mlp6/ADPL/software/cloud-dashboard/node-server/coverage/lcov-report/node-server/models/bucket-event.js.html

# All files / node-server/models bucket-event.js

100% Statements 4/4

100% Branches 0/0

100% Functions 0/0

100% Lines 4/4

1
2
3
4
5
6
7
8
9
10
11
12
13
14
15
16
17

1x
1x
1x

1x

/*
* bucket-event.js
* The schema to hold incoming bucket
* tip events from ADPL sites.
* @author: Suyash Kumar <suyashkumar2003@gmail.com>
*/
var mongoose = require('mongoose');
var Schema = mongoose.Schema;
var BucketEvent = new Schema({
coreid: {type: String, required: true, trim: true}, // Particle core id of sender
loc: {type: String, required: true, trim: true}, // Location identifier
time: {type: Date, required: true}, // Datetime of publish
data: {type: Number, required: false}, // typically a tip count since reset
});

module.exports = mongoose.model('BucketEvent', BucketEvent);

Code coverage generated by istanbul (http://istanbul-js.org/) at Wed Jan 18 2017 23:22:50 GMT-0800 (PST)
