mlp6/ADPL/software/cloud-dashboard/node-server/coverage/lcov-report/node-server/models/temperature-event.js.html

# All files / node-server/models temperature-event.js

100% Statements 4/4

100% Branches 0/0

100% Functions 0/0

100% Lines 4/4

1
2
3
4
5
6
7
8
9
10
11
12
13
14
15
16
17
18
19
20
21
22
23
24

2x
2x
2x

2x

/*
* temperature-event.js
* The schema (and model) to hold incoming
* temperature log events
* @author: Suyash Kumar <suyashkumar2003@gmail.com>
*/
var mongoose = require('mongoose');
var Schema = mongoose.Schema;
var TemperatureEvent = new Schema({
coreid: {type: String, required: true, trim: true}, // coreid of sender
loc: {type: String, required: true, trim: true}, // Location identifier
time: {type: Date, required: true}, // Time the data was published
temps: {
HXCI: {type: Number, required: false},
HXCO: {type: Number, required: false},
HTR: {type: Number, required: false},
HXHI: {type: Number, required: false},
HXHO: {type: Number, required: false},
},
valveStatus: {type: Boolean, required: false}, // Valve status at this event's time
});

module.exports = mongoose.model('TemperatureEvent', TemperatureEvent);

Code coverage generated by istanbul (http://istanbul-js.org/) at Wed Jan 18 2017 23:22:50 GMT-0800 (PST)
