mlp6/ADPL/hardware/picture_aids/FieldPics/IMG_2328.JPG

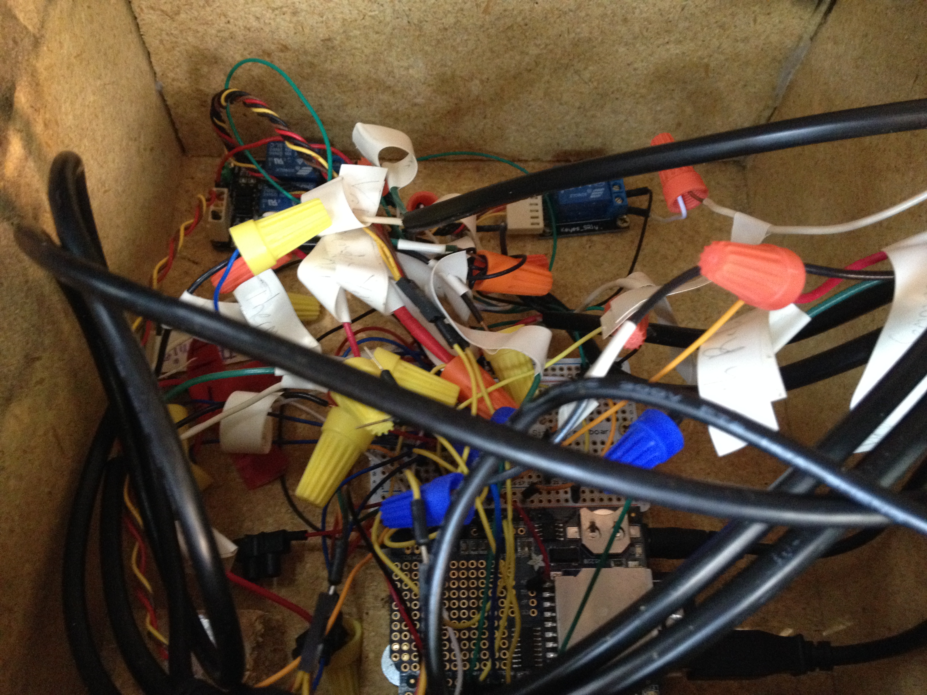
hardware/picture_aids/FieldPics/IMG_2328.JPG
