mlp6/ADPL/hardware/picture_aids/FieldPics/IMG_2395.JPG

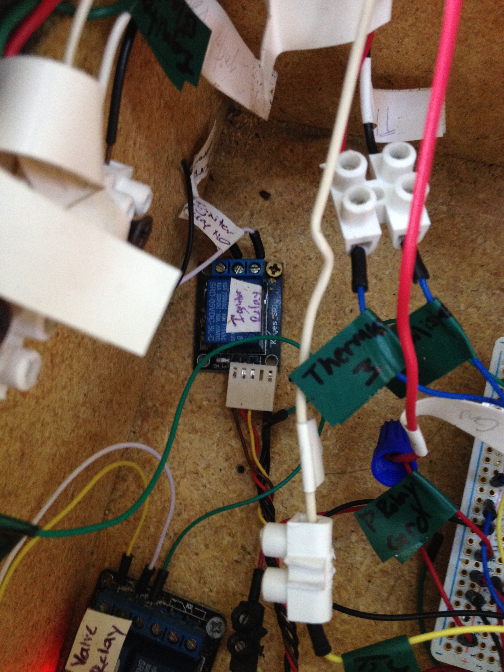
hardware/picture_aids/FieldPics/IMG_2395.JPG
