mlp6/ADPL/hardware/picture_aids/FieldPics/IMG_2436.JPG

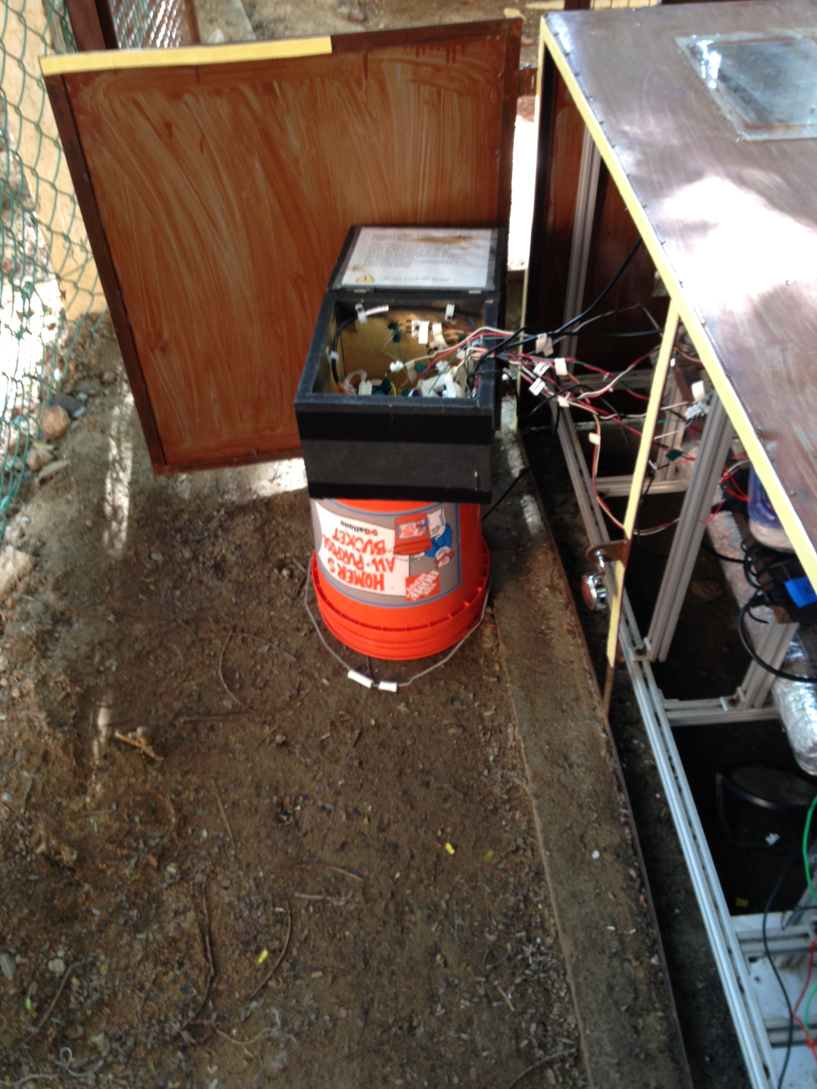
hardware/picture_aids/FieldPics/IMG_2436.JPG
