mlp6/ADPL/hardware/picture_aids/FieldPics/IMG_7628.JPG

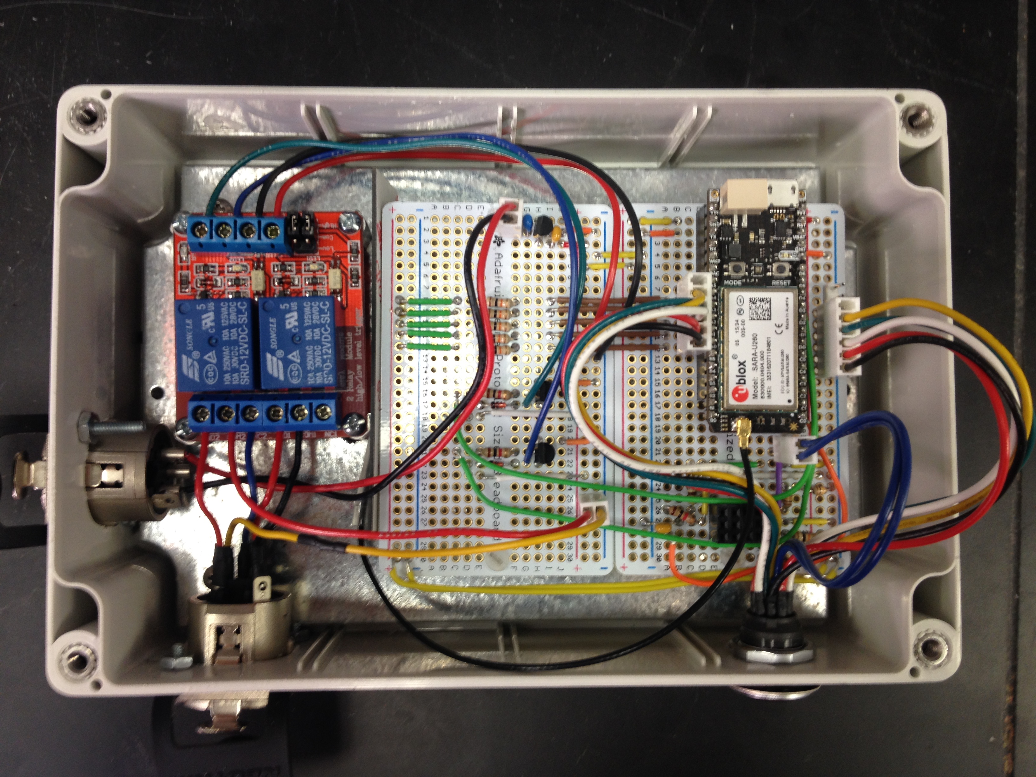
hardware/picture_aids/FieldPics/IMG_7628.JPG
