mlp6/ADPL/software/cloud-dashboard/node-server/coverage/lcov-report/node-server/tests/handle-device/test-data.js.html

# All files / node-server/tests/handle-device test-data.js

100% Statements 4/4

100% Branches 0/0

100% Functions 0/0

100% Lines 4/4

1
2
3
4
5
6
7
8
9
10
11
12
13

1x

1x

1x

1x

const sampleTempEvent = {data: '{"data":"HXCI:-73.9,HXCO:-75.7,HTR:-74.7,HXHI:-75.1,HXHO:-74.9,V:0","ttl":"60","published_at":"2017-01-19T06:45:44.999Z","coreid":"400057000a51343334363138"}'}

const sampleBucketEvent = {data: {"data":"0","ttl":"60","published_at":"2017-01-19T06:35:03.110Z","coreid":"2d0042000951343334363138"}};

const tempEventParsedData = {"HTR": "-74.7", "HXCI": "-73.9", "HXCO": "-75.7", "HXHI": "-75.1", "HXHO": "-74.9", "V": "0", "coreid": "400057000a51343334363138", "published_at": "2017-01-19T06:45:44.999Z"}

module.exports = {
sampleTempEvent,
sampleBucketEvent,
tempEventParsedData
}

Code coverage generated by istanbul (http://istanbul-js.org/) at Wed Jan 18 2017 23:22:50 GMT-0800 (PST)
