mlp6/ADPL/software/ADPL_electron/PinchValve.h

#ifndef ADPL_PINCHVALVE_H
#define ADPL_PINCHVALVE_H

class PinchValve{

    public:
        PinchValve(int dir_pin, int step_pin, int sleep_pin, int up_pin, int down_pin, int reset_pin);
        void shiftUp(double res);
        void shiftDown(double res);
        volatile bool moveup;
        volatile bool movedown;
        volatile bool isitup;
        unsigned long wait_time = 0;
        double position;
        double resolution;
        int clogCounting; // counts length of attempts to unclog
        void unclog(float unclog_resolution);
    private:
        int _dir_pin;
        int _step_pin;
        int _sleep_pin;
        static constexpr float _DELAY = 500; // variable in microseconds
        int _STEPSPERMM; // in this motor case 2mm per revolution, microstep of 8, 200 full steps per rotation, so 1600 for 2mm
        static constexpr int _MICROSTEP = 8; // Easy Driver has microstepping feature default of 8, could be adjusted with M1, M2, for now constant
        static constexpr int _MMPERTURN = 2; // constant for present motor
        static constexpr int _FULLSTEPSPERTURN = 200; // constant for present motor
        int turn_count;
};

#endif //ADPL_PINCHVALVE_H
