mlp6/ADPL/software/ADPL_electron/PublishDataCell.h

#ifndef PublishDataCell_h
#define PublishDataCell_h

#include "application.h"

class PublishDataCell {
public:
    bool publish(double HXCI, double HXCO, double HTR, double HXHI,
                 double HXHO, double Exhaust, int gasOn,
                 int bucket_tip_count);
private:
    char* fmt_string;
    char* fmt_string_no_bucket;
};

#endif
