mlp6/ADPL/software/ADPL_electron/PublishDataSD.h

#ifndef PublishDataSD_h
#define PublishDataSD_h

#include "application.h"
#include "SD/SdFat.h"

class PublishDataSD {
public:
    bool publish(double HXCI, double HXCO, double HTR, double HXHI, double HXHO,
                 double Exhaust, int gasOn, int bucket_tip_count, File sdFile);
    bool pushToCell(File sdFile);
    bool logError(int errorCode);
    bool inserted = false;
private:
    char* fmt_string_SD;
    char* fmt_string_no_bucket_SD;
    char* error_str;
    char* data_str;
};

#endif
