mlp6/ADPL/software/ADPL_electron/Ignitor.h

#ifndef Ignitor_h
#define Ignitor_h

#include "application.h"

class Ignitor {
    public:
        Ignitor(int pin);
        void fire();
        unsigned long timeLastFired;
        unsigned int repeatRefireAttempts = 0;
        unsigned int repeatRefireLimit = 5;
        unsigned long brokenTempDelay = 900000; // ms; delay to use when exhaust thermistor broken
        unsigned long refireDelay = 60000; // ms; delay between ignition attempts
        unsigned long resumeReignitionTime = 0; // ms; absolute time to reattempt ignition (set in main ino)
        unsigned long resumeReignitionDelay = 3600000; // ms; wait an hour after repeatRefireLimit attemps to ignite
        bool allow = true; // allow attempted ignition
    private:
        int _pin;
        static const int _ignitor_on_time = 10000;   // ms; keep on for 10 s

};

#endif
