mlp6/ADPL/software/ADPL_electron/Ignitor.cpp

/* 
 * Ignitor.cpp - ignitor control
 */

#include "application.h"
#include "Ignitor.h"

Ignitor::Ignitor(int pin) {
    pinMode(pin, OUTPUT);
    _pin = pin;
    timeLastFired = 0;
}

void Ignitor::fire() {
    digitalWrite(_pin, HIGH);
    delay(_ignitor_on_time);
    digitalWrite(_pin, LOW);
    timeLastFired = millis();
}
